greatmanokonkwo/vics/describe/imgs/22.jpg

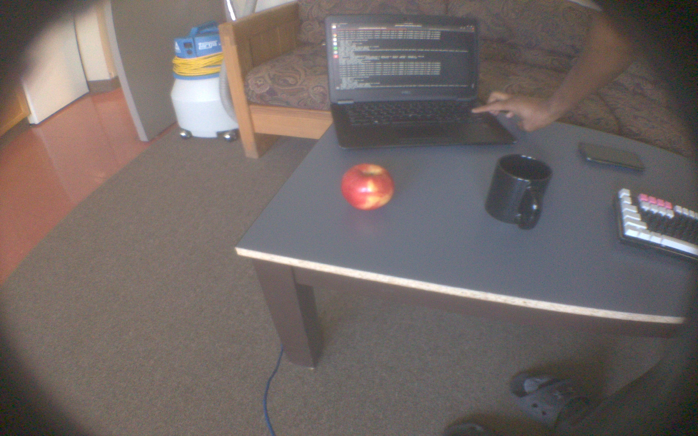
describe/imgs/22.jpg
