greatmanokonkwo/vics/devs_and_utils/picam.py

import cv2

class picam:
	cam = None
	
	def __init__(self, width, height):
		self.cam = cv2.VideoCapture(self.gstreamer_pipeline(width, height), cv2.CAP_GSTREAMER)
	
	def gstreamer_pipeline(self, capture_width, capture_height):
		return (
			"nvarguscamerasrc sensor_mode=0 ! "
			"video/x-raw(memory:NVMM), "
			"width=(int)3820, height=(int)2464, "
			"format=(string)NV12, framerate=(fraction)21/1 ! "
			"nvvidconv flip-method=0 ! "
			"video/x-raw, width=(int)%d, height=(int)%d, format=(string)BGRx ! "
			"videoconvert ! "
			"video/x-raw, format=(string)BGR ! appsink"
			% (
				capture_width,
				capture_height
			)
		)

	def save_image(self, path, img=None):
		if img is None:
			cv2.imwrite(path, self.capture_image())
		else:
			cv2.imwrite(path, img)

	def capture_image(self):
		if self.cam.isOpened():
			for i in range(12):
				ret_val, img = self.cam.read()
			return img
		else:
			print("Unable to open camera")

	def cleanup(self):
		self.cam.release()

if __name__=="__main__":
	cam = picam(width=2464, height=2464)
	cam.save_image(input("Name of image: "))
	cam.cleanup()
