greatmanokonkwo/vics/devs_and_utils/test_mpu.py

import os
import sys
import time
import smbus 
import numpy as np 

from imusensor.MPU9250 import MPU9250
from imusensor.filters import madgwick

sensorfusion = madgwick.Madgwick(0.5)

address = 0x68
bus = smbus.SMBus(1)
imu = MPU9250.MPU9250(bus, address)
imu.begin()

calib_file = "calib.json"

imu.loadCalibDataFromFile(calib_file)	

count = 0
currTime = time.time()

time_cnt = 0

start_time = time.time()
initial_yaw = 0

# Sensor fusion testing for getting angles
while True:

	imu.readSensor()
	for i in range(10):
		newTime = time.time()
		dt = newTime - currTime
		currTime = newTime

		sensorfusion.updateRollPitchYaw(imu.AccelVals[0], imu.AccelVals[1], imu.AccelVals[2], imu.GyroVals[0], imu.GyroVals[1], imu.GyroVals[2], imu.MagVals[0], imu.MagVals[1], imu.MagVals[2], dt)

	if time_cnt == 2:
		time_cnt = 0	
		#print(f"Accelorometer: {imu.AccelVals[0]} {imu.AccelVals[1]} {imu.AccelVals[2]}")
		#print(f"Gyroscope: {imu.GyroVals[0]} {imu.GyroVals[1]} {imu.GyroVals[2]}")
		#print(f"Magnetometer: {imu.MagVals[0]} {imu.MagVals[1]} {imu.MagVals[2]}")
		print (f"Yaw : {round(sensorfusion.yaw/10)*10}")
	time_cnt+=1
	time.sleep(0.01)

"""
# Testing for halt determination

sample_count = 0
midline = -9.8
thresh = 0.6
max_val = -999

currTime = time.time()
while True:
	imu.readSensor()
	
	sample = imu.AccelVals[2]
	max_val = max(max_val, sample)

	newTime = time.time()

	if newTime - currTime >= 1:
		if (max_val - midline) > thresh:
			print(max_val, 0)
		else:
			print(max_val, 1)
	
		max_val = -999

		currTime = newTime
"""
