greatmanokonkwo/vics/devs_and_utils/audio_utils.py

"""download and/or process data"""
import torch
import torch.nn as nn
import torchaudio
import pandas as pd
from sonopy import power_spec, mel_spec, mfcc_spec, filterbanks


class MFCC(nn.Module):

    def __init__(self, sample_rate, fft_size=400, window_stride=(400, 200), num_filt=40, num_coeffs=40):
        super(MFCC, self).__init__()
        self.sample_rate = sample_rate
        self.window_stride = window_stride
        self.fft_size = fft_size
        self.num_filt = num_filt
        self.num_coeffs = num_coeffs
        self.mfcc = lambda x: mfcc_spec(
            x, self.sample_rate, self.window_stride,
            self.fft_size, self.num_filt, self.num_coeffs
        )
    
    def forward(self, x):
        return torch.Tensor(self.mfcc(x.squeeze(0).numpy())).transpose(0, 1).unsqueeze(0)


def get_featurizer(sample_rate):
    return MFCC(sample_rate=sample_rate)


class RandomCut(nn.Module):
    """Augmentation technique that randomly cuts start or end of audio"""

    def __init__(self, max_cut=10):
        super(RandomCut, self).__init__()
        self.max_cut = max_cut

    def forward(self, x):
        """Randomly cuts from start or end of batch"""
        side = torch.randint(0, 1, (1,))
        cut = torch.randint(1, self.max_cut, (1,))
        if side == 0:
            return x[:-cut,:,:]
        elif side == 1:
            return x[cut:,:,:]


class SpecAugment(nn.Module):
    """Augmentation technique to add masking on the time or frequency domain"""

    def __init__(self, rate, policy=3, freq_mask=2, time_mask=4):
        super(SpecAugment, self).__init__()

        self.rate = rate

        self.specaug = nn.Sequential(
            torchaudio.transforms.FrequencyMasking(freq_mask_param=freq_mask),
            torchaudio.transforms.TimeMasking(time_mask_param=time_mask)
        )

        self.specaug2 = nn.Sequential(
            torchaudio.transforms.FrequencyMasking(freq_mask_param=freq_mask),
            torchaudio.transforms.TimeMasking(time_mask_param=time_mask),
            torchaudio.transforms.FrequencyMasking(freq_mask_param=freq_mask),
            torchaudio.transforms.TimeMasking(time_mask_param=time_mask)
        )

        policies = { 1: self.policy1, 2: self.policy2, 3: self.policy3 }
        self._forward = policies[policy]

    def forward(self, x):
        return self._forward(x)

    def policy1(self, x):
        probability = torch.rand(1, 1).item()
        if self.rate > probability:
            return  self.specaug(x)
        return x

    def policy2(self, x):
        probability = torch.rand(1, 1).item()
        if self.rate > probability:
            return  self.specaug2(x)
        return x

    def policy3(self, x):
        probability = torch.rand(1, 1).item()
        if probability > 0.5:
            return self.policy1(x)
        return self.policy2(x)

def collate_fn(data):
    """Batch and pad wakeword data"""

    rand_cut = RandomCut(max_cut=10)
    mfccs = []
    labels = []
    for d in data:
        mfcc, label = d
        mfccs.append(mfcc.squeeze(0).transpose(0, 1))
        labels.append(label)

    # pad mfccs to ensure all tensors are same size in the time dim
    mfccs = nn.utils.rnn.pad_sequence(mfccs, batch_first=True)  # batch, seq_len, feature
    mfccs = mfccs.transpose(0, 1) # seq_len, batch, feature
    mfccs = rand_cut(mfccs)
    #print(mfccs.shape)
    labels = torch.Tensor(labels)
    return mfccs, labels
